MinoduLCN/minodulcn.github.io/assets/images/backoffice_products_table.jpg

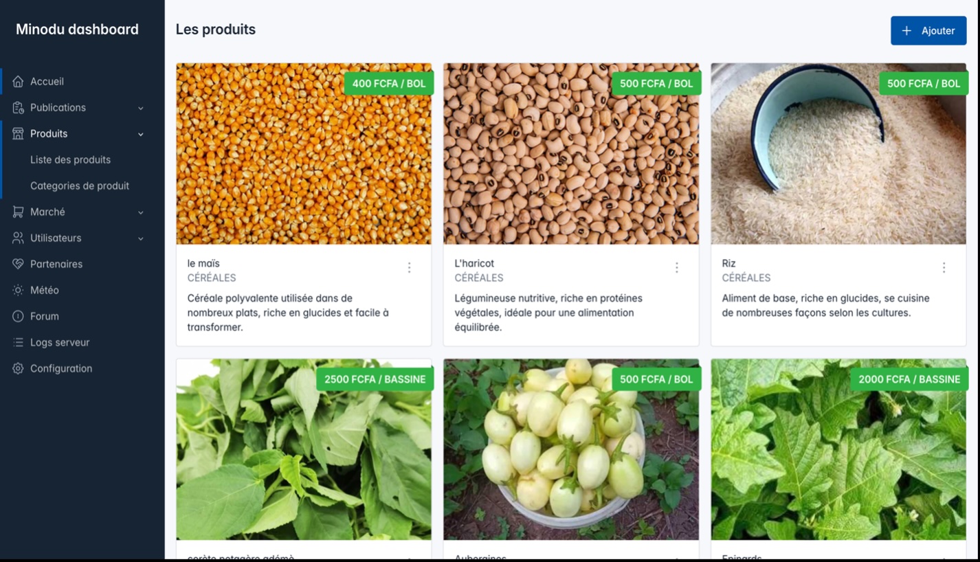
assets/images/backoffice_products_table.jpg
