MinoduLCN/minodulcn.github.io/assets/images/digital_inspiration.png

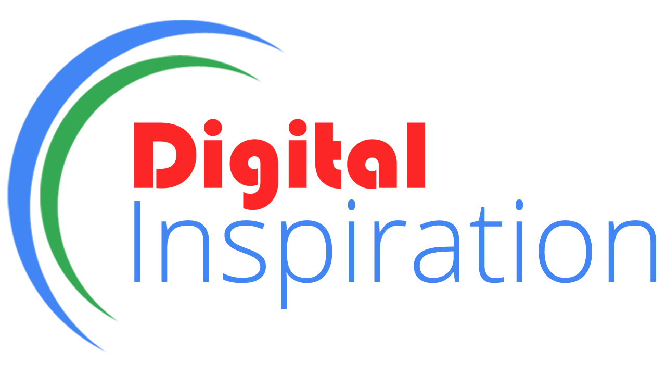
assets/images/digital_inspiration.png
