MinoduLCN/minodulcn.github.io/assets/images/Fona.png

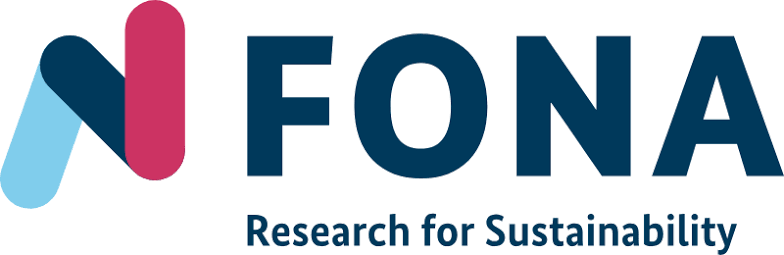
assets/images/Fona.png
