MinoduLCN/minodulcn.github.io/assets/images/lutz-reiter.png

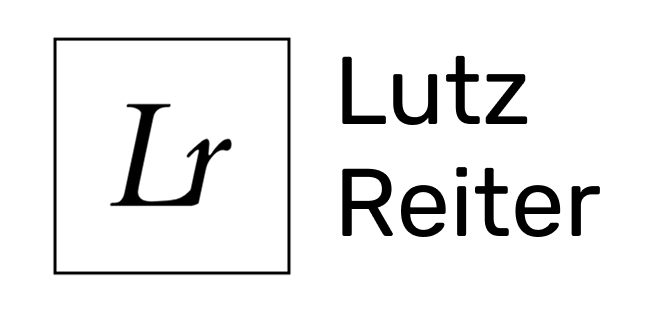
assets/images/lutz-reiter.png
