MinoduLCN/minodulcn.github.io/assets/images/StevesonS_17.jpg

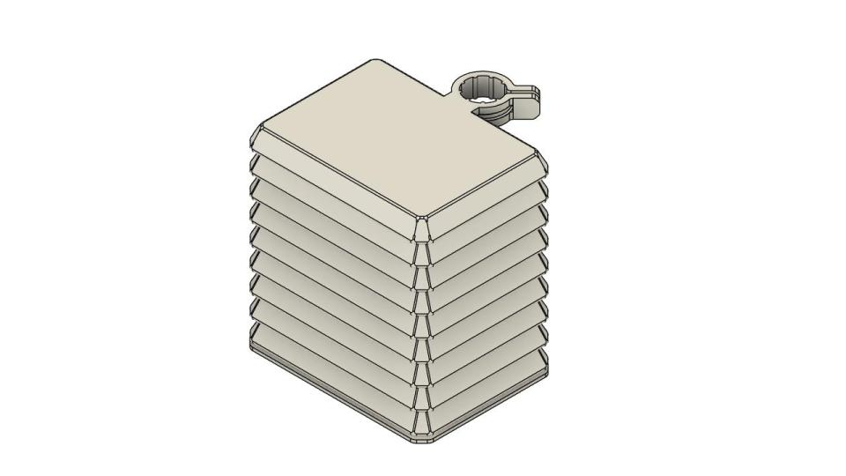
assets/images/StevesonS_17.jpg
