MinoduLCN/minodulcn.github.io/assets/3dFiles/Latch_x02.stl

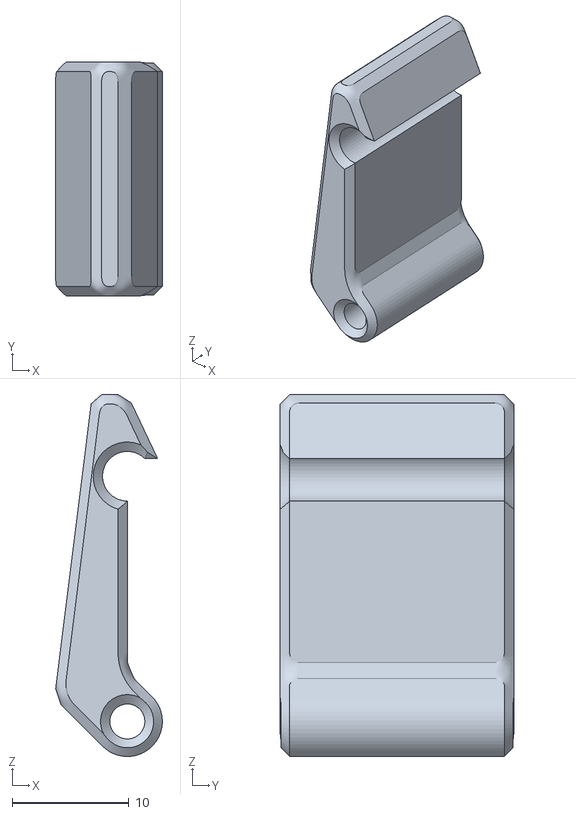
[picture p114: CAD file, 2026-06-15]
assets/3dFiles/Latch_x02.stl
9.14 x 20.0 x 31.0
