MinoduLCN/minodulcn.github.io/assets/3dFiles/Base_x01.stl

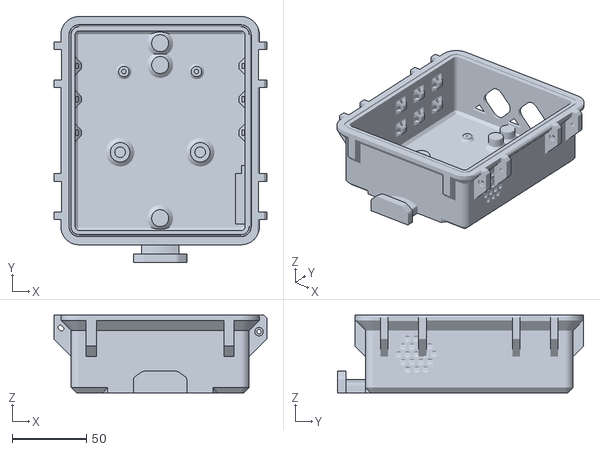
[picture p115: CAD file, 2026-06-15]
assets/3dFiles/Base_x01.stl
143.5 x 165.9 x 52.5
